faridyagubbayli/tech_challenge_ws1819/IMG_0311.jpg

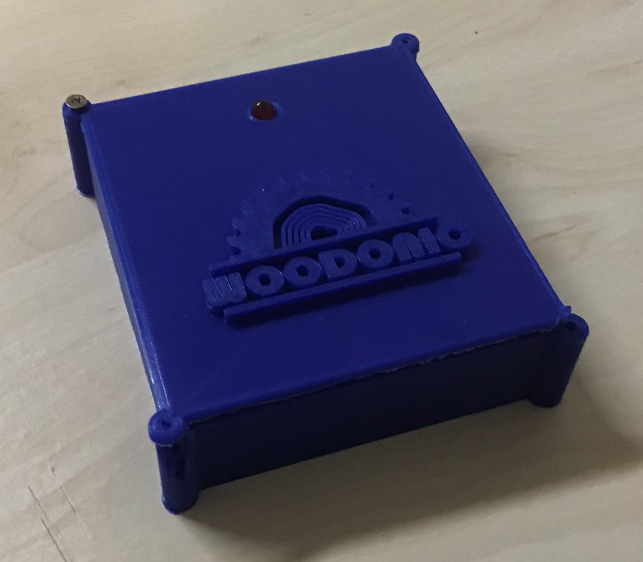
IMG_0311.jpg
